doryan04/AngelWings-keyboard/cases/Pic/case2.png

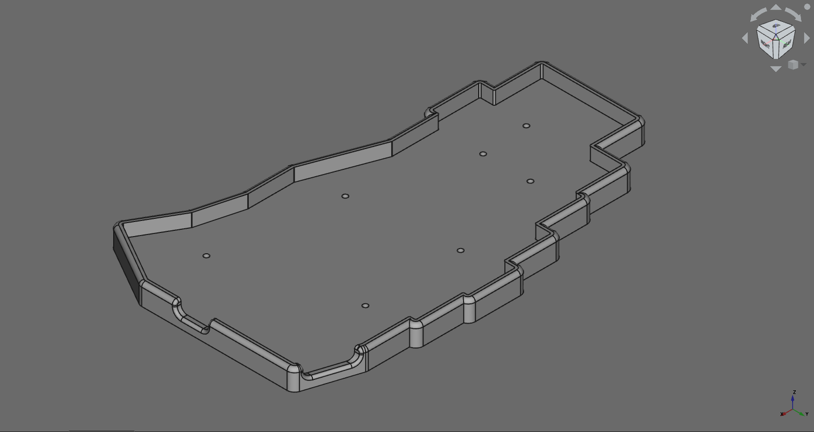
cases/Pic/case2.png
