doryan04/AngelWings-keyboard/cases/Pic/case4.png

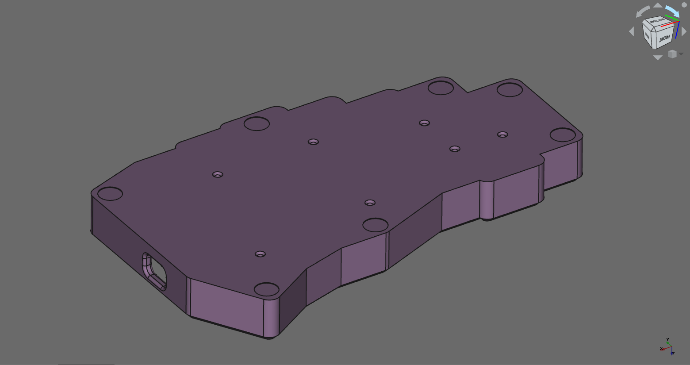
cases/Pic/case4.png
