doryan04/AngelWings-keyboard/photos/awf(1).jpg

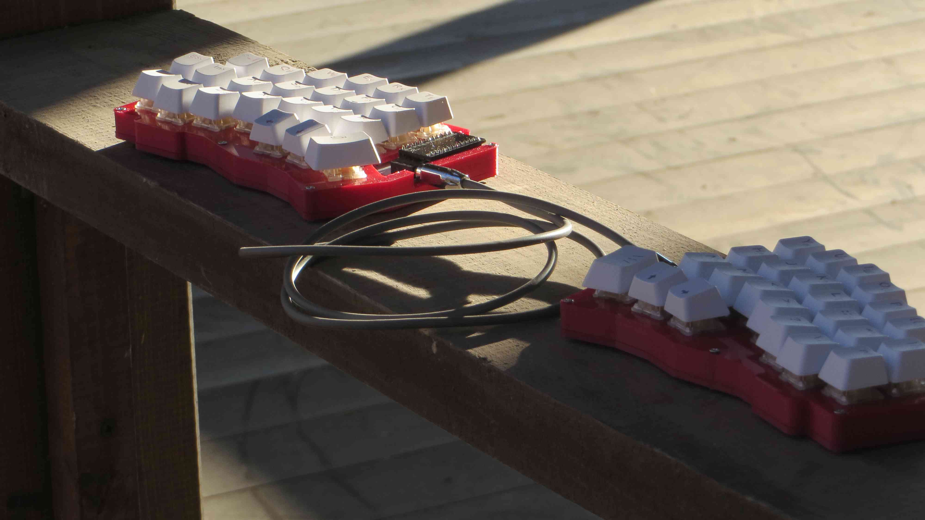
photos/awf(1).jpg
