doryan04/AngelWings-keyboard/photos/bottomplate.png

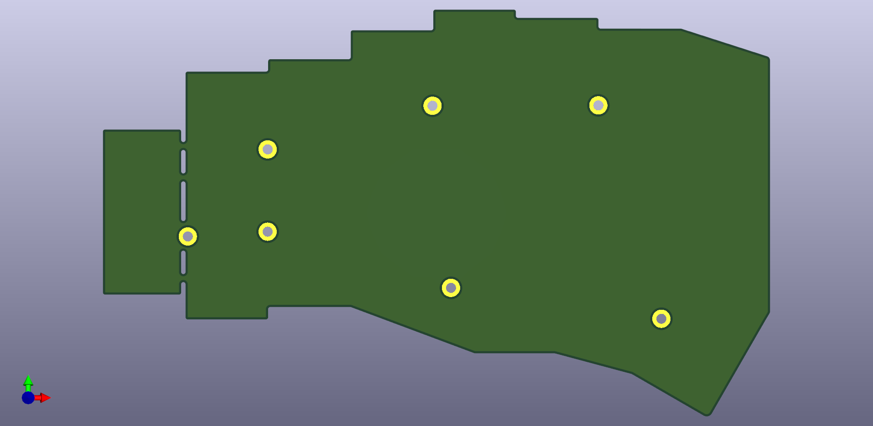
photos/bottomplate.png
