doryan04/AngelWings-keyboard/photos/pcb.png

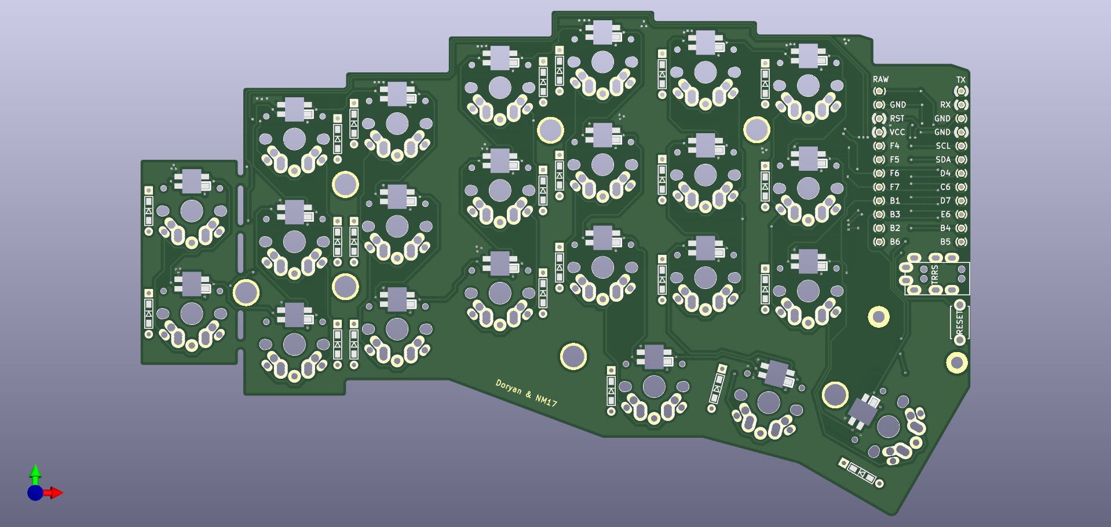
photos/pcb.png
