doryan04/AngelWings-keyboard/thumb/via.png

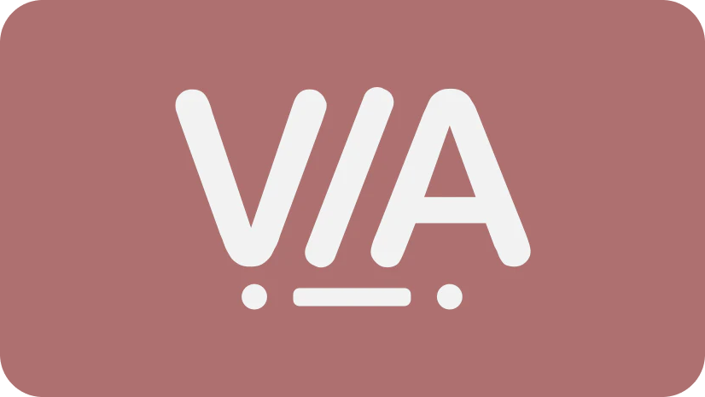
thumb/via.png
